minirevollo/Zyliss_Swift_Dry_Ersatzteil/IMG/Salatschleuder_zyliss_dry (3).jpg

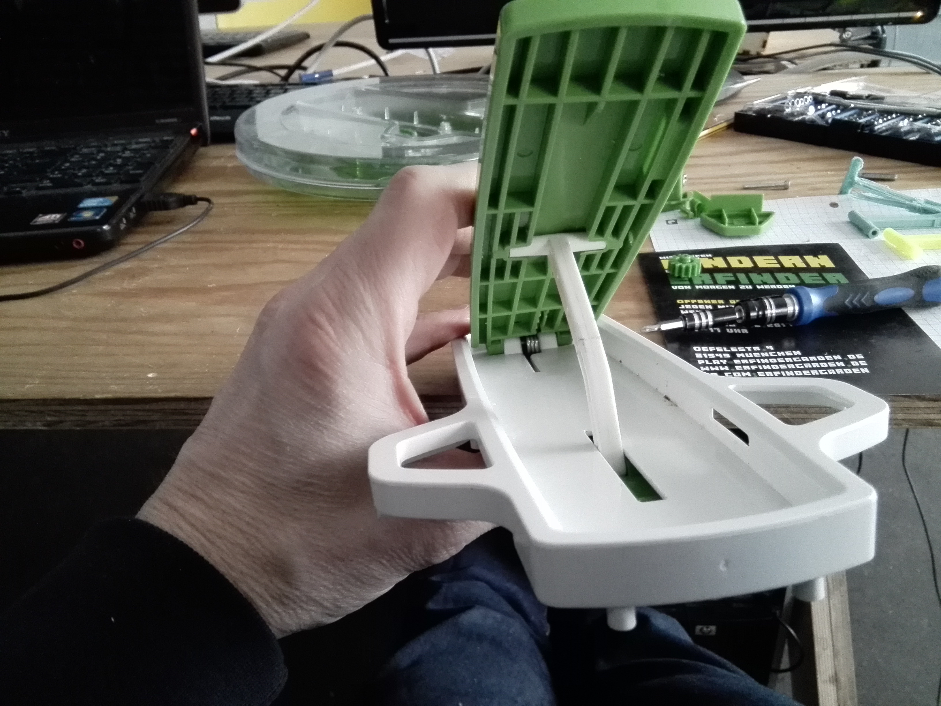
IMG/Salatschleuder_zyliss_dry (3).jpg
