minirevollo/Zyliss_Swift_Dry_Ersatzteil/IMG/Salatschleuder_zyliss_dry (7).jpg

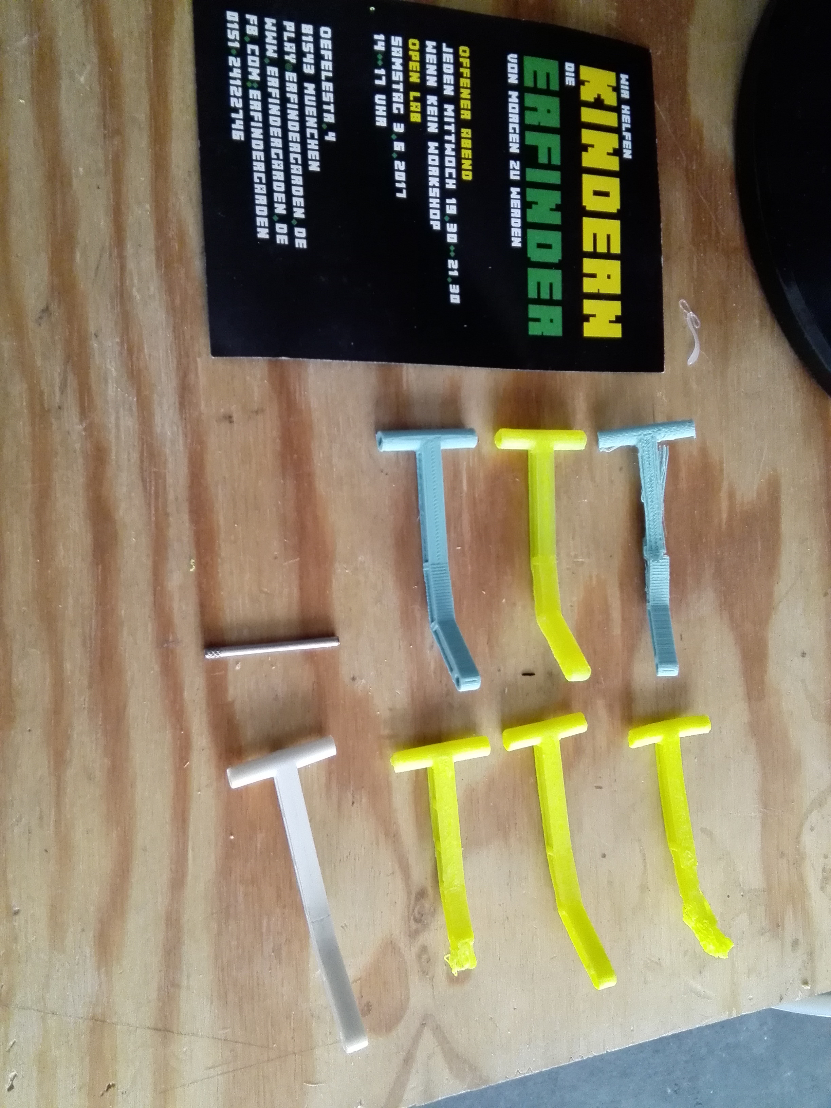
IMG/Salatschleuder_zyliss_dry (7).jpg
