minirevollo/Zyliss_Swift_Dry_Ersatzteil/IMG/Salatschleuder_zyliss_dry (9).jpg

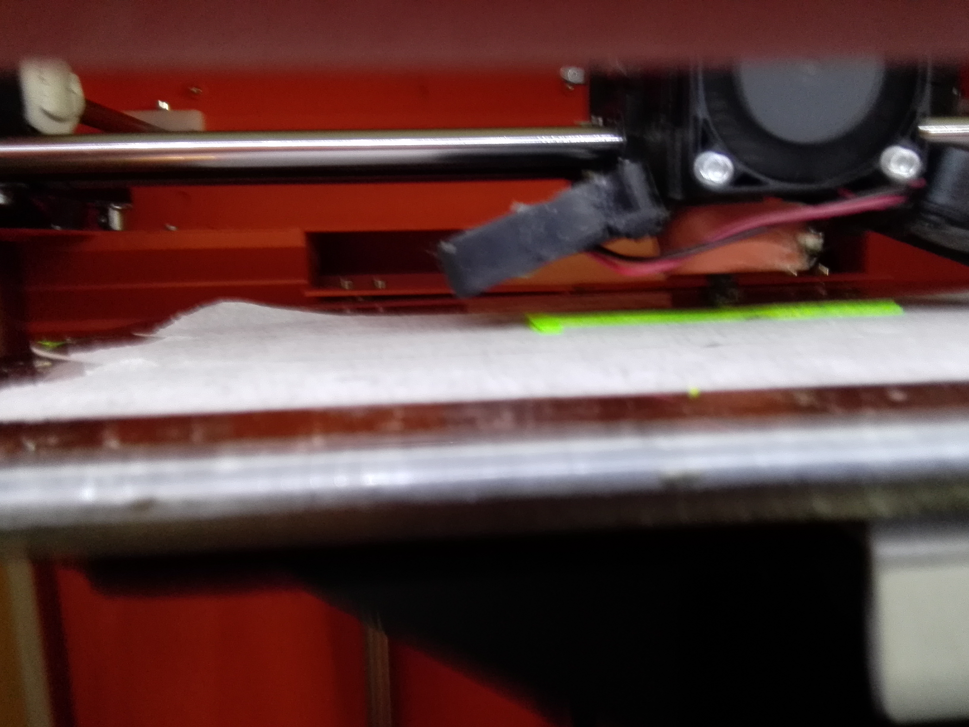
IMG/Salatschleuder_zyliss_dry (9).jpg
